peterdk31/bc250_ws2812b_controller/daemon/power_remote.hpp

#pragma once

#include <math.h>
#include <stdio.h>
#include <string.h>
#include <memory>
#include <string>
#include <vector>

#include "config_edit.hpp"
#include "config_loader.hpp"
#include "protocol.hpp"
#include "sink.hpp"
#include "views.hpp"

// The power switch's half of the BLE dashboard (README "BLE remote", "Power
// switch"): the config's `power_switch` block as far as a phone may change
// it. The block is otherwise flash-time — pins and the enable go onto the
// receiver's `pwrcfg` partition with `make flash-pwr`, and stay there: a pin
// the machine's power hangs on is not re-pinned from a sofa. Its four
// TUNINGS, though, are values the switch's task reads on every poll, so they
// are pushed to the receiver at runtime (proto::CMD_PWR_TUNING) at startup,
// on a live reload and after an edit, the way the fans' standalone settings
// are — the receiver applies them at once and persists them, and this file
// stays the source of truth on a running machine. One pin goes the same
// way: `pins.wake`, the wake input (README "Waking from an OpenPuck"), which
// can do nothing but power the machine on (proto::CMD_PWR_WAKE; the receiver
// checks the pin against its own facts and keeps the one it has when it
// refuses). `short_press` is this daemon's own (the command a short press
// runs, daemon/output/serial_sink.hpp) and is applied to the link at once.
//
// Like the fans and the strip this is JSON text the receiver relays unread;
// the view goes out as VIEW_POWER, an edit comes back as MSG_EDIT for it,
// is validated here against the same ranges tools/pwrcfg.py enforces at
// flash time, written into the block through config_edit.hpp, pushed, and
// answered with the new view. The shape, all keys as the config spells them
// (`wake` is `pins.wake`, flattened):
//
//     { "editable": true,                 // config writable and has the block
//       "hold_seconds": 2, "boot_timeout_seconds": 10,
//       "sense_low_mv": 800, "sense_high_mv": 2000,
//       "wake": 20,                              // a GPIO, or null = no wake input
//       "short_press": "systemctl poweroff" }   // or null
//
// An edit is a partial object of the same keys (not "editable"). A config
// with no power_switch block sends no view at all: the phone then talks to
// the receiver directly (its control op), and the daemon has no say.
namespace pwrcfg
{
class Remote
{
public:
    // the top-level config block this module owns; like the fans', nothing
    // in it feeds the strip (see fans::Controller::BLOCK)
    static constexpr const char* BLOCK = "power_switch";
    // ...and the view it owns on the dashboard (protocol.hpp)
    static const uint8_t VIEW = proto::VIEW_POWER;

    // read the block. cfg is held onto (its values are edited in place so the
    // running tree matches the file); writer is the config file's editor,
    // null = read-only.
    void load(Config& cfg, cfgedit::Writer* writer)
    {
        cfg_ = &cfg;
        writer_ = writer;
        const json::Value* block = cfg.root().find(BLOCK);
        hasBlock_ = block && block->isObject();
        tuningOk_ = false;
        enabled_ = false;
        shortPress_ = ""; // a block removed on reload takes its command with it
        if (!hasBlock_)
            return;

        if (const json::Value* en = block->find("enabled"))
            enabled_ = json::toBool(*en, false);
        auto num = [&](const char* key, double def) {
            const json::Value* v = block->find(key);
            return v && v->isNumber() ? v->number : def;
        };
        hold_ = num("hold_seconds", 2);
        boot_ = num("boot_timeout_seconds", 10);
        low_ = (int)num("sense_low_mv", 800);
        high_ = (int)num("sense_high_mv", 2000);
        if (const json::Value* sp = block->find("short_press"))
            if (sp->isString())
                shortPress_ = sp->text;

        // pins.wake: a GPIO or null. Anything else (or no pins object) is a
        // block the flasher would refuse — not pushed, and the phone's pick
        // then goes to the receiver alone
        wake_ = -1;
        wakeOk_ = false;
        if (const json::Value* pins = block->find("pins"))
            if (pins->isObject())
                if (const json::Value* w = pins->find("wake"))
                {
                    if (w->type == json::Value::Type::Null)
                        wakeOk_ = true;
                    else if (w->isNumber() && w->number == floor(w->number) && w->number >= 0 &&
                             w->number <= WAKE_MAX)
                    {
                        wake_ = (int)w->number;
                        wakeOk_ = true;
                    }
                }
        if (!wakeOk_)
            fprintf(stderr, "power_switch.pins.wake: expected a GPIO number or null — not pushed "
                            "to the receiver, and the dashboard can't set it\n");

        // the four are the receiver's to run; a block pwrcfg.py refused at
        // flash time can still be hand-edited into nonsense afterwards, and
        // that must not be pushed (the receiver would refuse it anyway, but
        // silently, on a board with no console)
        std::string why;
        tuningOk_ = checkTuning(hold_, boot_, low_, high_, why);
        if (!tuningOk_)
            fprintf(stderr, "power_switch: %s — the receiver keeps its stored tunings, "
                            "and the dashboard's power settings are read-only\n", why.c_str());
    }

    bool writable() const { return hasBlock_ && tuningOk_ && writer_ && writer_->writable(); }
    const std::string& shortPress() const { return shortPress_; }
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
